bastl-instruments/kastle2/code/src/common/dsp/math/lookup_qmath_sine.hpp

/*
MIT License

Copyright (c) 2024 Vaclav Mach (Bastl Instruments)

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
THE SOFTWARE IS PROVIDED "AS IS", WITHOUT WARRANTY OF ANY KIND, EXPRESS OR
IMPLIED, INCLUDING BUT NOT LIMITED TO THE WARRANTIES OF MERCHANTABILITY,
FITNESS FOR A PARTICULAR PURPOSE AND NONINFRINGEMENT. IN NO EVENT SHALL THE
AUTHORS OR COPYRIGHT HOLDERS BE LIABLE FOR ANY CLAIM, DAMAGES OR OTHER
LIABILITY, WHETHER IN AN ACTION OF CONTRACT, TORT OR OTHERWISE, ARISING FROM,
OUT OF OR IN CONNECTION WITH THE SOFTWARE OR THE USE OR OTHER DEALINGS IN THE
SOFTWARE.
*/

#pragma once


namespace kastle2
{

/**
 * @file lookup_qmath_sine.h
 * @ingroup dsp_math
 * @brief Sine table for fast sine calculation.
 * @author Vaclav Mach (Bastl Instruments)
 * @date 2024-04-12
 */

#include <cstdint>

#define QMATH_SINE_TABLE_SIZE 4096
#define QMATH_SINE_TABLE_SHIFT_Q31 19 // (32 - 13)
#define QMATH_SINE_TABLE_SHIFT_Q15 3 // (16 - 13)

const int32_t qmath_sine_table[QMATH_SINE_TABLE_SIZE] = {
    0, 3294197, 6588387, 9882561,
    13176712, 16470832, 19764913, 23058947,
    26352928, 29646846, 32940695, 36234466,
    39528151, 42821744, 46115236, 49408620,
    52701887, 55995030, 59288042, 62580914,
    65873638, 69166208, 72458615, 75750851,
    79042909, 82334782, 85626460, 88917937,
    92209205, 95500255, 98791081, 102081675,
    105372028, 108662134, 111951983, 115241570,
    118530885, 121819921, 125108670, 128397125,
    131685278, 134973122, 138260647, 141547847,
    144834714, 148121241, 151407418, 154693240,
    157978697, 161263783, 164548489, 167832808,
    171116733, 174400254, 177683365, 180966058,
    184248325, 187530159, 190811551, 194092495,
    197372981, 200653003, 203932553, 207211624,
    210490206, 213768293, 217045878, 220322951,
    223599506, 226875535, 230151030, 233425984,
    236700388, 239974235, 243247518, 246520228,
    249792358, 253063900, 256334847, 259605191,
    262874923, 266144038, 269412525, 272680379,
    275947592, 279214155, 282480061, 285745302,
    289009871, 292273760, 295536961, 298799466,
    302061269, 305322361, 308582734, 311842381,
    315101295, 318359466, 321616889, 324873555,
    328129457, 331384586, 334638936, 337892498,
    341145265, 344397230, 347648383, 350898719,
    354148230, 357396906, 360644742, 363891730,
    367137861, 370383128, 373627523, 376871039,
    380113669, 383355404, 386596237, 389836160,
    393075166, 396313247, 399550396, 402786604,
    406021865, 409256170, 412489512, 415721883,
    418953276, 422183684, 425413098, 428641511,
    431868915, 435095303, 438320667, 441545000,
    444768294, 447990541, 451211734, 454431865,
    457650927, 460868912, 464085813, 467301622,
    470516330, 473729932, 476942419, 480153784,
    483364019, 486573117, 489781069, 492987869,
    496193509, 499397982, 502601279, 505803394,
    509004318, 512204045, 515402566, 518599875,
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
}
